mohammedawwad22/Self-Balancing-Robot/Solidworks/mpu-6050-imu-sensor-1.snapshot.5/Base.SLDPRT

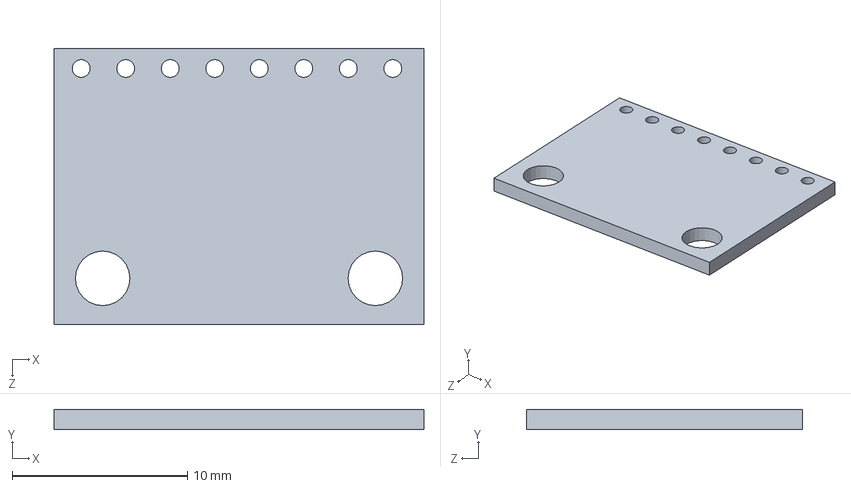
[picture p37: CAD file, 2020-05-28]
Solidworks/mpu-6050-imu-sensor-1.snapshot.5/Base.SLDPRT
21.1 x 1.14 x 15.7 mm
