mohammedawwad22/Self-Balancing-Robot/Solidworks/mpu-6050-imu-sensor-1.snapshot.5/Resistor black.SLDPRT

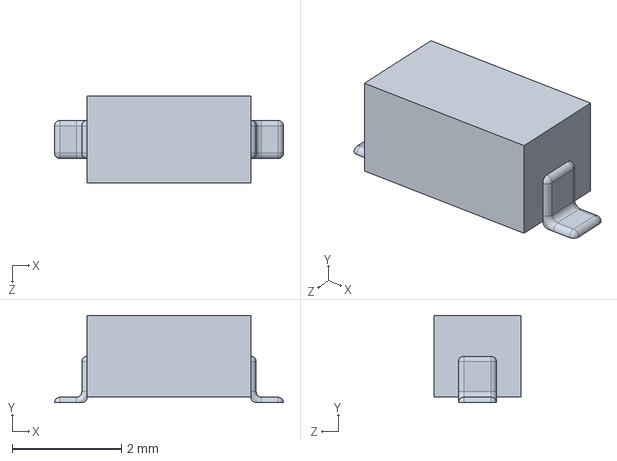
[picture p38: CAD file, 2020-05-28]
Solidworks/mpu-6050-imu-sensor-1.snapshot.5/Resistor black.SLDPRT
4.20 x 1.60 x 1.60 mm
