mohammedawwad22/Self-Balancing-Robot/Solidworks/mpu-6050-imu-sensor-1.snapshot.5/sensor chip.SLDPRT

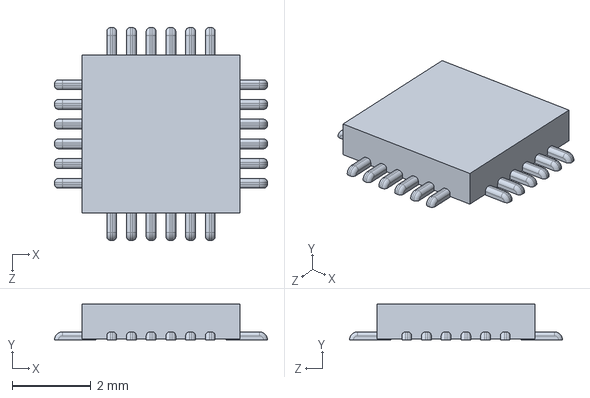
[picture p39: CAD file, 2020-05-28]
Solidworks/mpu-6050-imu-sensor-1.snapshot.5/sensor chip.SLDPRT
5.40 x 0.9 x 5.40 mm
