mohammedawwad22/Self-Balancing-Robot/Solidworks/mpu-6050-imu-sensor-1.snapshot.5/Small LED.SLDPRT

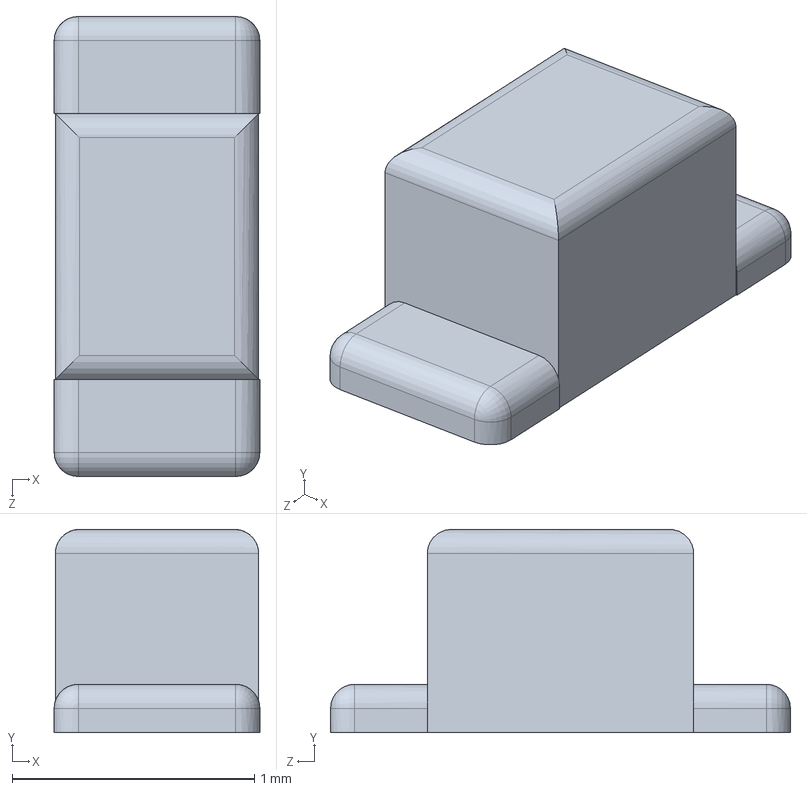
[picture p40: CAD file, 2020-05-28]
Solidworks/mpu-6050-imu-sensor-1.snapshot.5/Small LED.SLDPRT
0.85 x 0.84 x 1.90 mm
